dbloemhard/ESP32_Transmitter_for_ELRS/Assets/Joystick Wiring 1.jpg

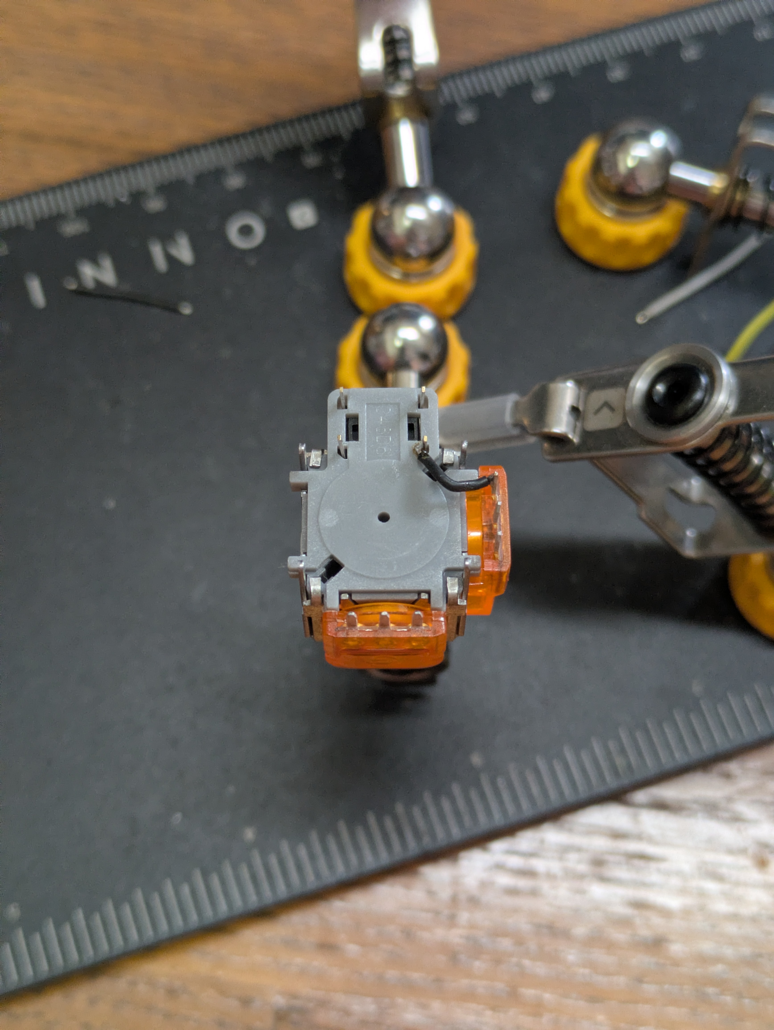
Assets/Joystick Wiring 1.jpg
