dbloemhard/ESP32_Transmitter_for_ELRS/Assets/Ready for Assembly 1.jpg

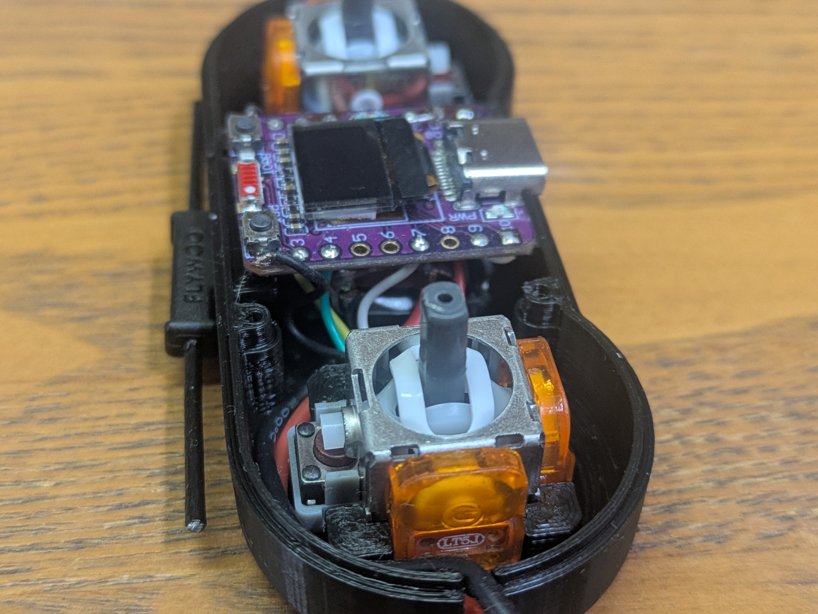
Assets/Ready for Assembly 1.jpg
