dbloemhard/ESP32_Transmitter_for_ELRS/Assets/Wiring Diagram Complete.png

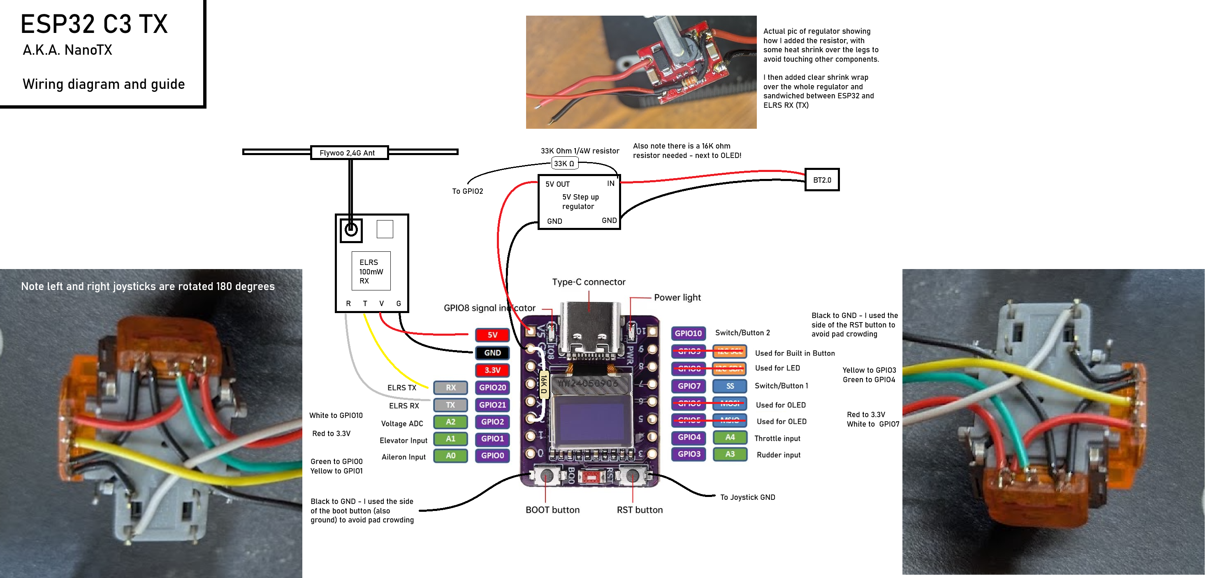
Assets/Wiring Diagram Complete.png
