dbloemhard/ESP32_Transmitter_for_ELRS/oled.h

#pragma once
#ifndef OLED_H
#define OLED_H
//#define TIMINGDEBUG
/*
 * This file is part of ESP32C3-TX
 *
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
 * ESP32C3-TX is distributed in the hope that it will be useful,
 * but WITHOUT ANY WARRANTY; without even the implied warranty of
 * MERCHANTABILITY or FITNESS FOR A PARTICULAR PURPOSE.  See the
 * GNU General Public License for more details.
 * <http://www.gnu.org/licenses/>.
 */
#include <Wire.h>
#include "elrs.h"
#include "params.h"
#include <U8g2lib.h>

extern U8G2_SSD1306_72X40_ER_F_HW_I2C display;
 //----- OLED Screen setup  -------------------
const int OLED_WIDTH = 72;
const int OLED_HEIGHT = 40;
const int OLED_X_OFFSET = 0; //28; // Standard alignment for 0.42" 72x40 on 128px space
const int OLED_Y_OFFSET = 0; //12; // Adjusted to shift the 40px matrix vertically if needed

enum displayState {MAIN_PAGE, ELRS_STATS, ELRS_MENU, CHANNEL_OUTPUTS, CHANNEL_MENU, BT_JOYSTICK, MODEL_FINDER, CALIBRATION};
extern displayState currentScreen; 
extern displayState lastScreen;
enum menuMode { MENU_BROWSE, MENU_EDIT };
extern menuMode menuState;

void initDisplay();
void drawBootLogo();
void clearScreen();
void nextScreen();

void drawHomeScreen(float voltage, int telemetryState, uint8_t uplinkLQ, int16_t channels[],int16_t minChannelValue,int16_t maxChannelValue);
void drawElrsStatsScreen(const ELRS& elrs);
void drawChannelOutputsScreen(int16_t channels[], int16_t min, int16_t max);
void drawBtJoystickScreen();
void drawBtTxScreen();

void drawCalibrationScreen(int stage, int secondsLeft);

void drawMenuScreen(const ParamCollection& menu);
void drawScrollingMenuValue(const char* text, int textX, int textY, int displayAreaWidth);
void drawMenuItem(const crsfParameter& menuItem, int offsetX, int offsetY);
void animateMenu(const ParamCollection& menu);
void drawEditValue(const crsfParameter& menuItem, int32_t editValue, int offsetX, int offsetY);
void animateEditValue(const ParamCollection& menu);
void drawScrollingPopupText(const char* text, int textX, int textY, int displayAreaWidth);
void drawPopup(const ParamCollection& menu);
int  navigateMenu(ParamCollection &menu, uint8_t direction);
void drawModelFinderScreen(int raw, int avg, int strength);

void drawMessage(char title[], char line1[], char line2[]);


// NanoTX Logo
// Dimensions: 72 x 40 pixels
const uint8_t nanotx_logo_72x40[] U8X8_PROGMEM = {
  B00000000, B00000000, B00000000, B00000000, B00000000, B00000000, B00000000, B00000000, B00000000, 
  B00000000, B00000000, B00000000, B00000000, B00000000, B00000000, B00000000, B00000000, B00000000, 
  B00000000, B00000000, B00000000, B00000000, B00000000, B00000000, B00000000, B00000000, B00000000, 
  B00000000, B00000000, B00000000, B00000000, B00000000, B00000000, B00000000, B00000000, B00000000,
  B00000000, B00000000, B00000000, B00000000, B00000000, B00000000, B00000000, B00000000, B00000000, 
  B00000000, B00000000, B00000000, B00000000, B00000000, B00000000, B00000000, B00000000, B00000000, 
  B00000000, B00000000, B00000000, B00000000, B00000000, B00000000, B00000000, B00001100, B00000000, 
  B00000000, B00000000, B00000000, B00000000, B00000000, B00000000, B00000000, B00000010, B00001000,
  B00000000, B00000000, B00000000, B00000000, B00000000, B00000000, B00000000, B00001010, B00010000, 
  B00000000, B00000000, B00000000, B00000000, B00000000, B00000000, B00000000, B00100101, B00100100, 
  B00000000, B00000000, B00000000, B00000000, B00000000, B00000000, B00000000, B10010100, B00101001, 
  B00000000, B11111100, B11111111, B11111111, B11111111, B11111111, B11111111, B11010100, B00101001,
  B10000000, B11111111, B11111111, B11111111, B11111111, B11111111, B11111111, B11000100, B00101000, 
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
                                 B00001000, 
                                 B00011100, 
                                 B00101010, 
                                 B00011000, 
                                 B00001000,
                                 B00000000 };
#endif
